RedClaws1800/dspico-RedKey/dspico-artwork-design/guides/high-spec-options.jpg

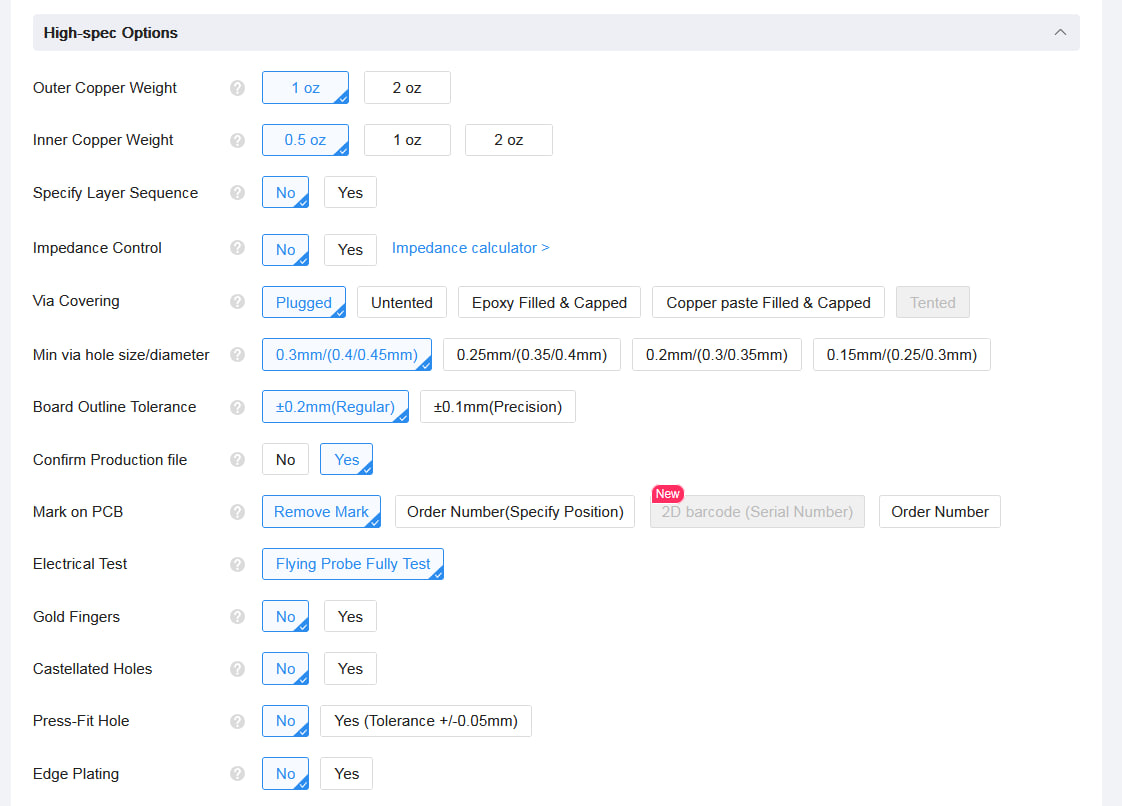
dspico-artwork-design/guides/high-spec-options.jpg
