RedClaws1800/dspico-RedKey/dspico-artwork-design/guides/high-spec-options.png

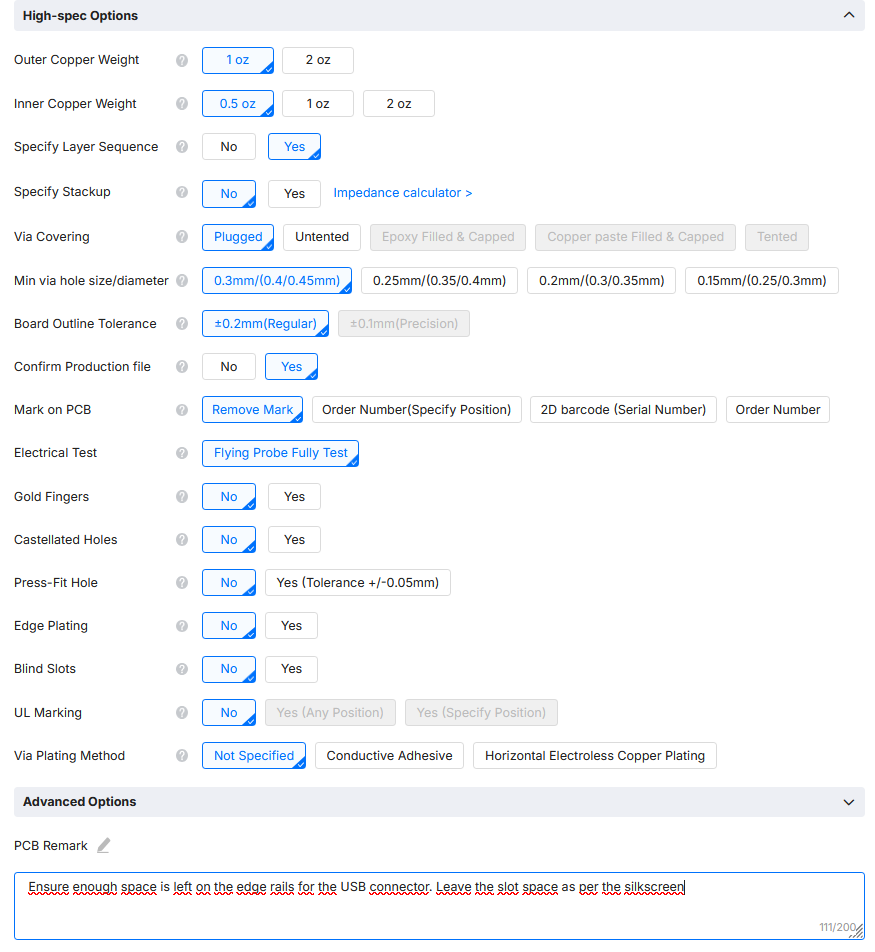
dspico-artwork-design/guides/high-spec-options.png
