RedClaws1800/dspico-RedKey/dspico-artwork-design/guides/pcb-specifications.jpg

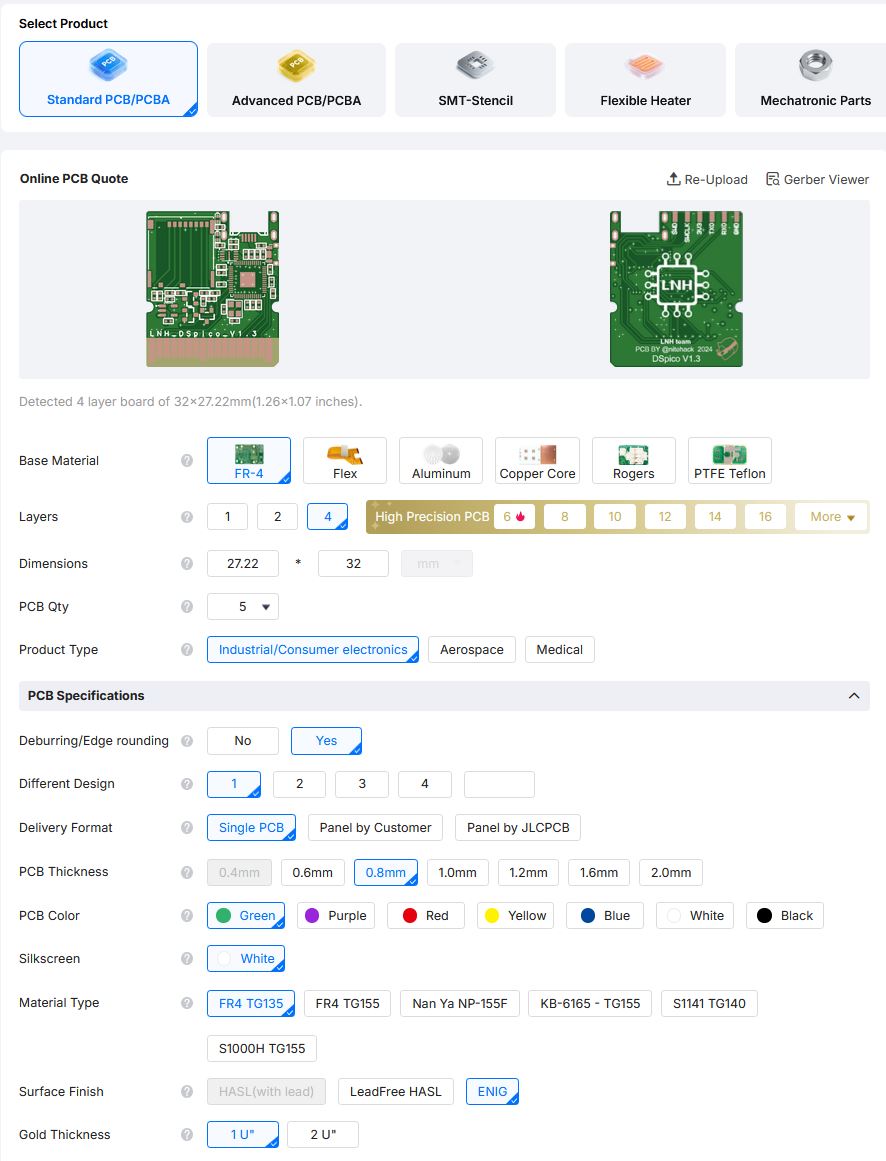
dspico-artwork-design/guides/pcb-specifications.jpg
