RedClaws1800/dspico-RedKey/dspico-artwork-design/stickers/dspico-white-sticker.png

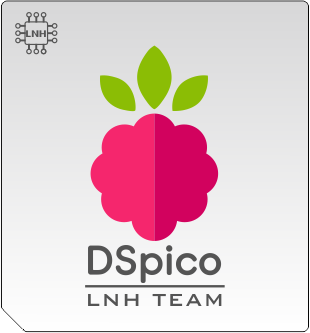
dspico-artwork-design/stickers/dspico-white-sticker.png
