RedClaws1800/dspico-RedKey/dspico-artwork-design/guides/3d-order.jpg

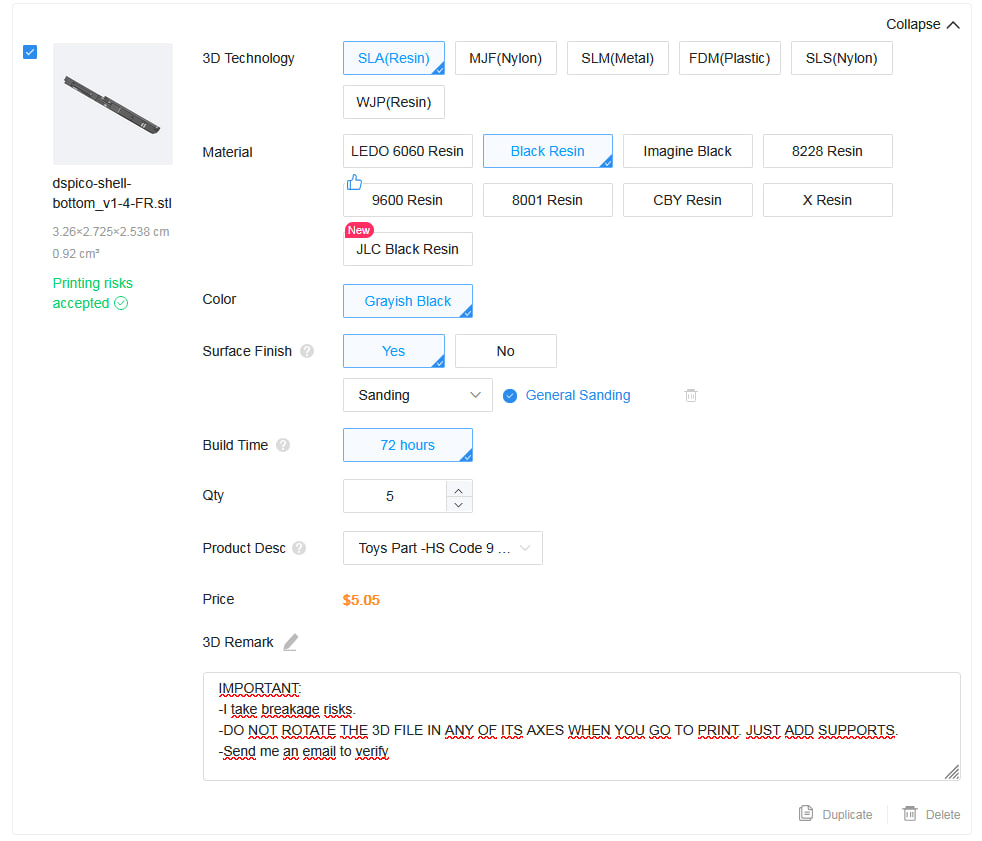
dspico-artwork-design/guides/3d-order.jpg
