RedClaws1800/dspico-RedKey/dspico-artwork-design/guides/bom-jlcpcb.PNG

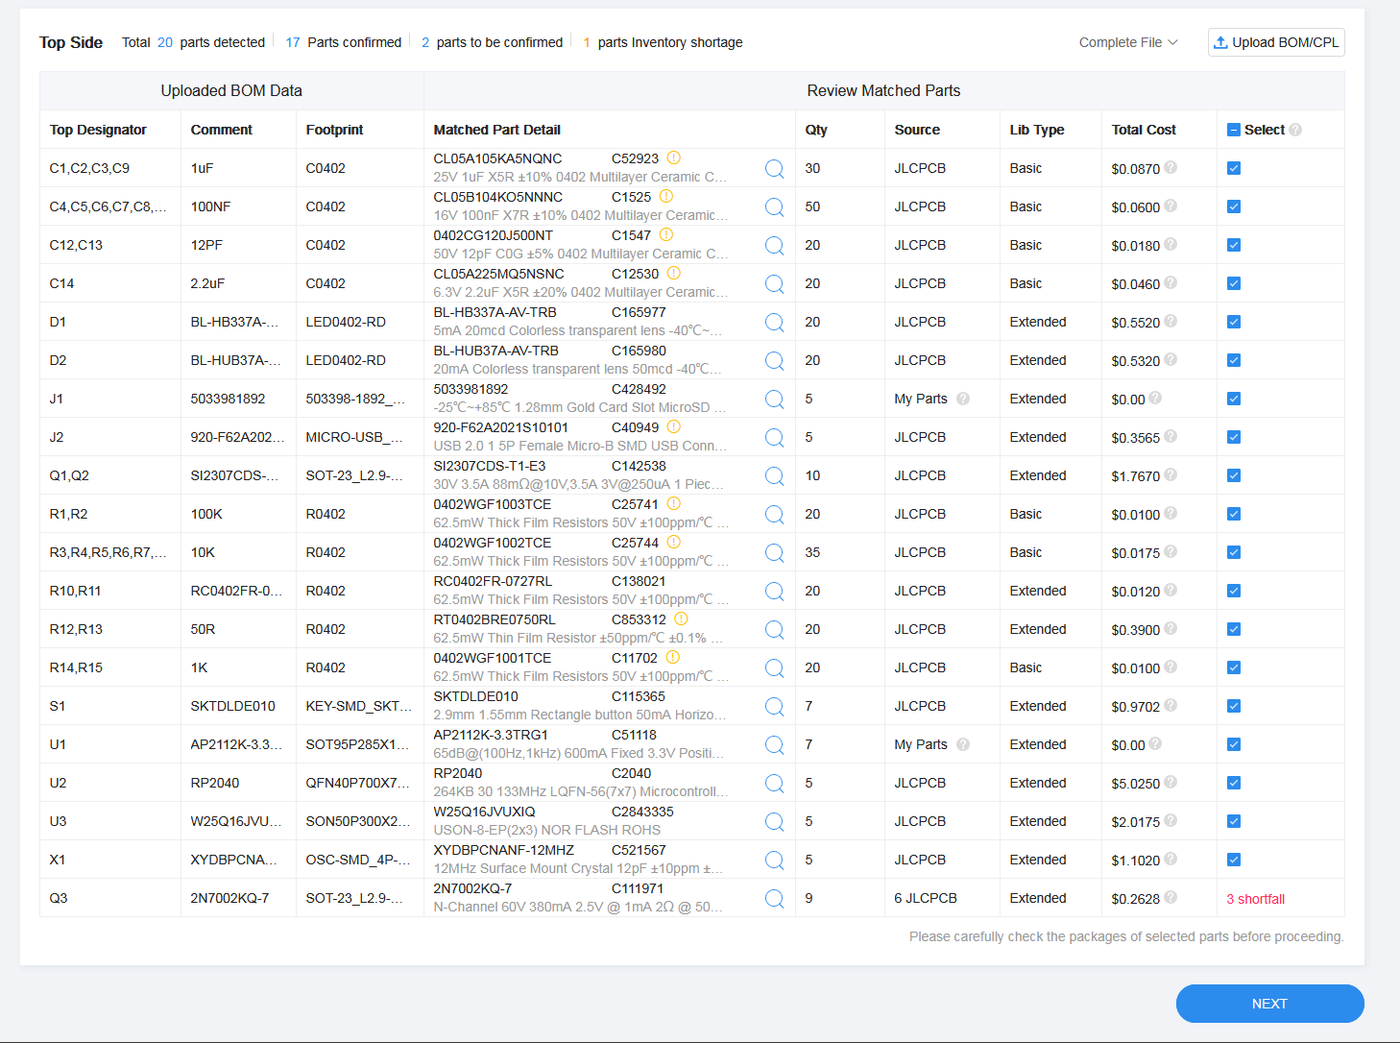
dspico-artwork-design/guides/bom-jlcpcb.PNG
