RedClaws1800/dspico-RedKey/dspico-artwork-design/guides/smt-order.png

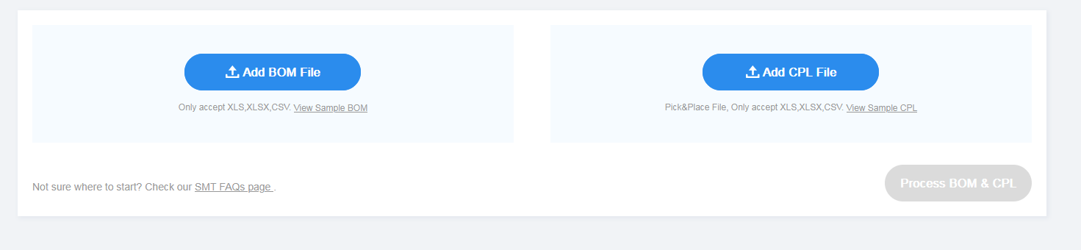
dspico-artwork-design/guides/smt-order.png
