RedClaws1800/dspico-RedKey/dspico-artwork-design/guides/bottom-shell-orientation.png

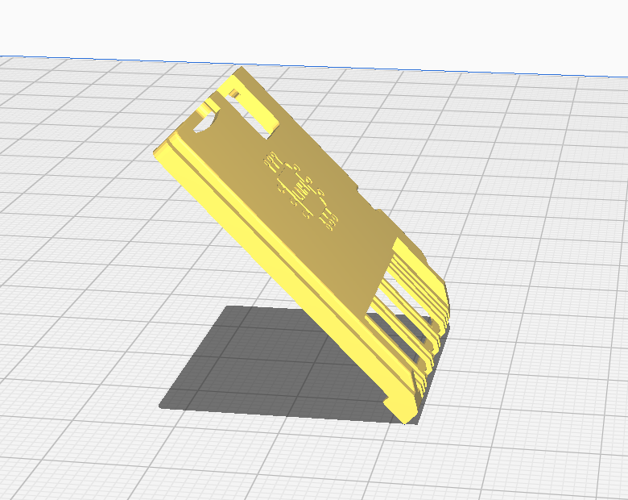
dspico-artwork-design/guides/bottom-shell-orientation.png
