RedClaws1800/dspico-RedKey/dspico-artwork-design/guides/layer-sequence.jpg

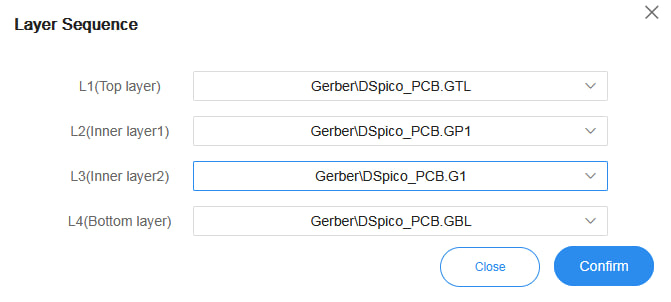
dspico-artwork-design/guides/layer-sequence.jpg
