RedClaws1800/dspico-RedKey/dspico-artwork-design/guides/pcba-assembly.PNG

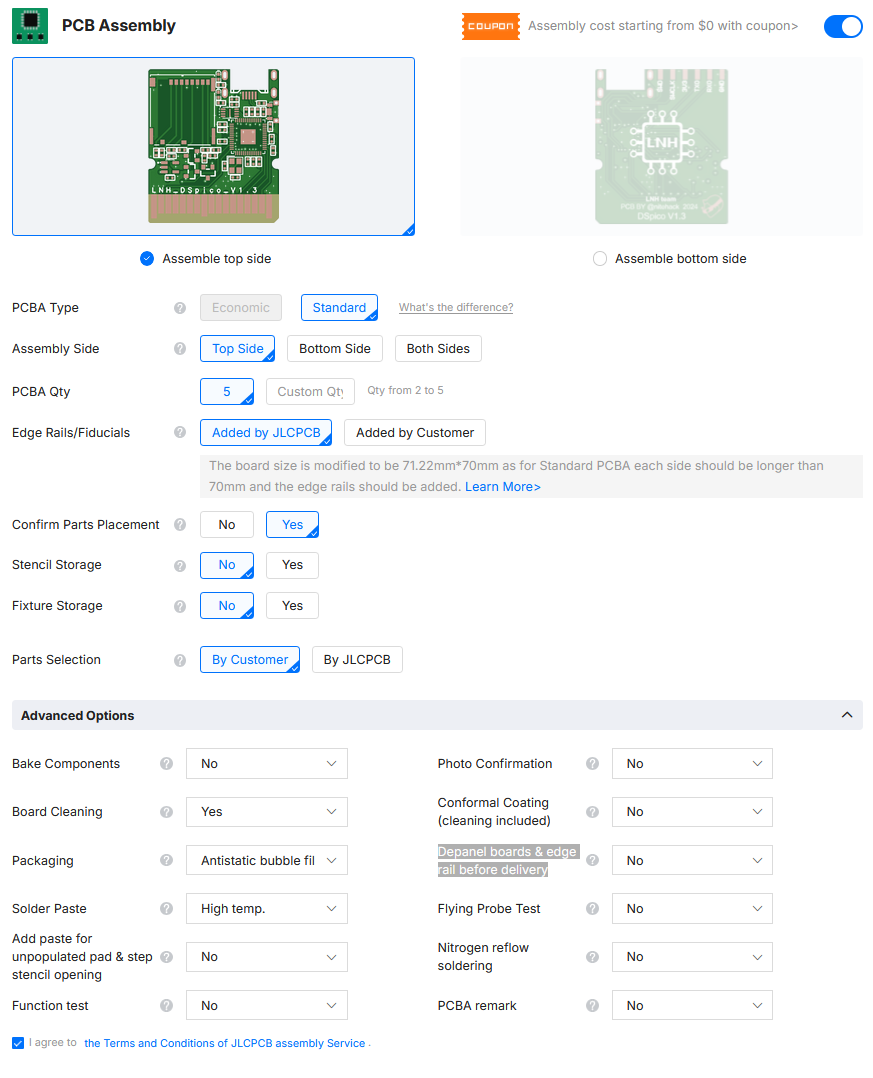
dspico-artwork-design/guides/pcba-assembly.PNG
