RedClaws1800/dspico-RedKey/dspico-artwork-design/guides/placement-dspico.jpg

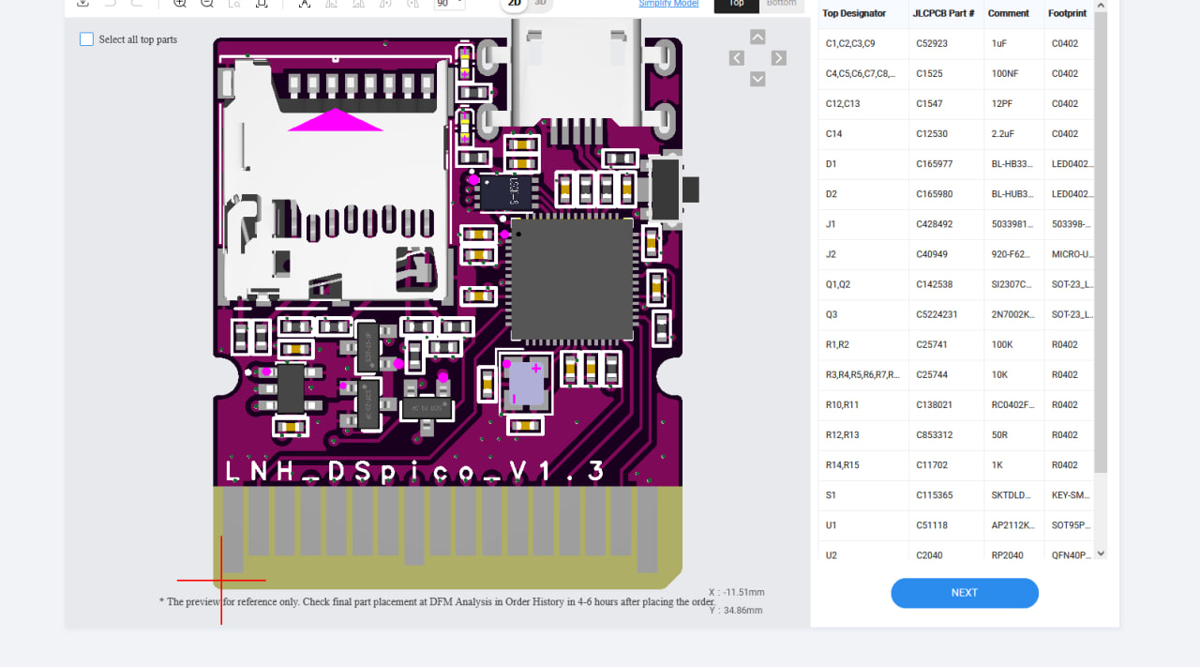
dspico-artwork-design/guides/placement-dspico.jpg
