RedClaws1800/dspico-RedKey/dspico-artwork-design/guides/space-rails.png

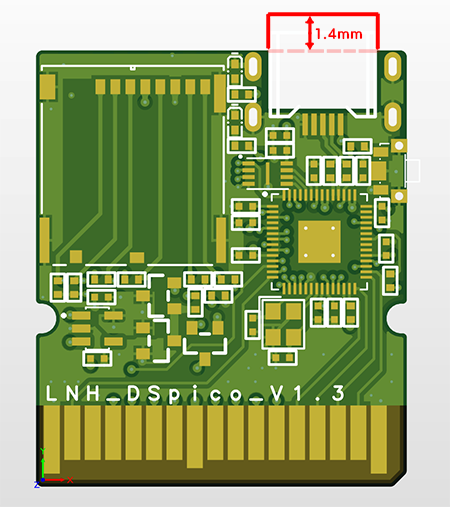
dspico-artwork-design/guides/space-rails.png
