RedClaws1800/dspico-RedKey/dspico-artwork-design/guides/issue-rails-shell.jpg

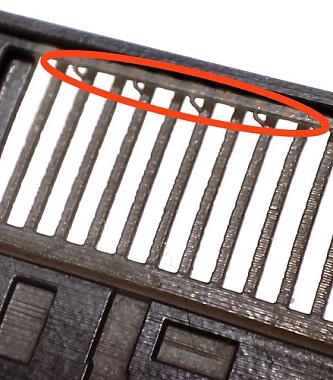
dspico-artwork-design/guides/issue-rails-shell.jpg
